manhoosbilli1/Iphone7-batteryless-MOD/qianli_reverse_engineering.kicad_sch

## KiCad design qianli_reverse_engineering.kicad_sch (2024-02-01)

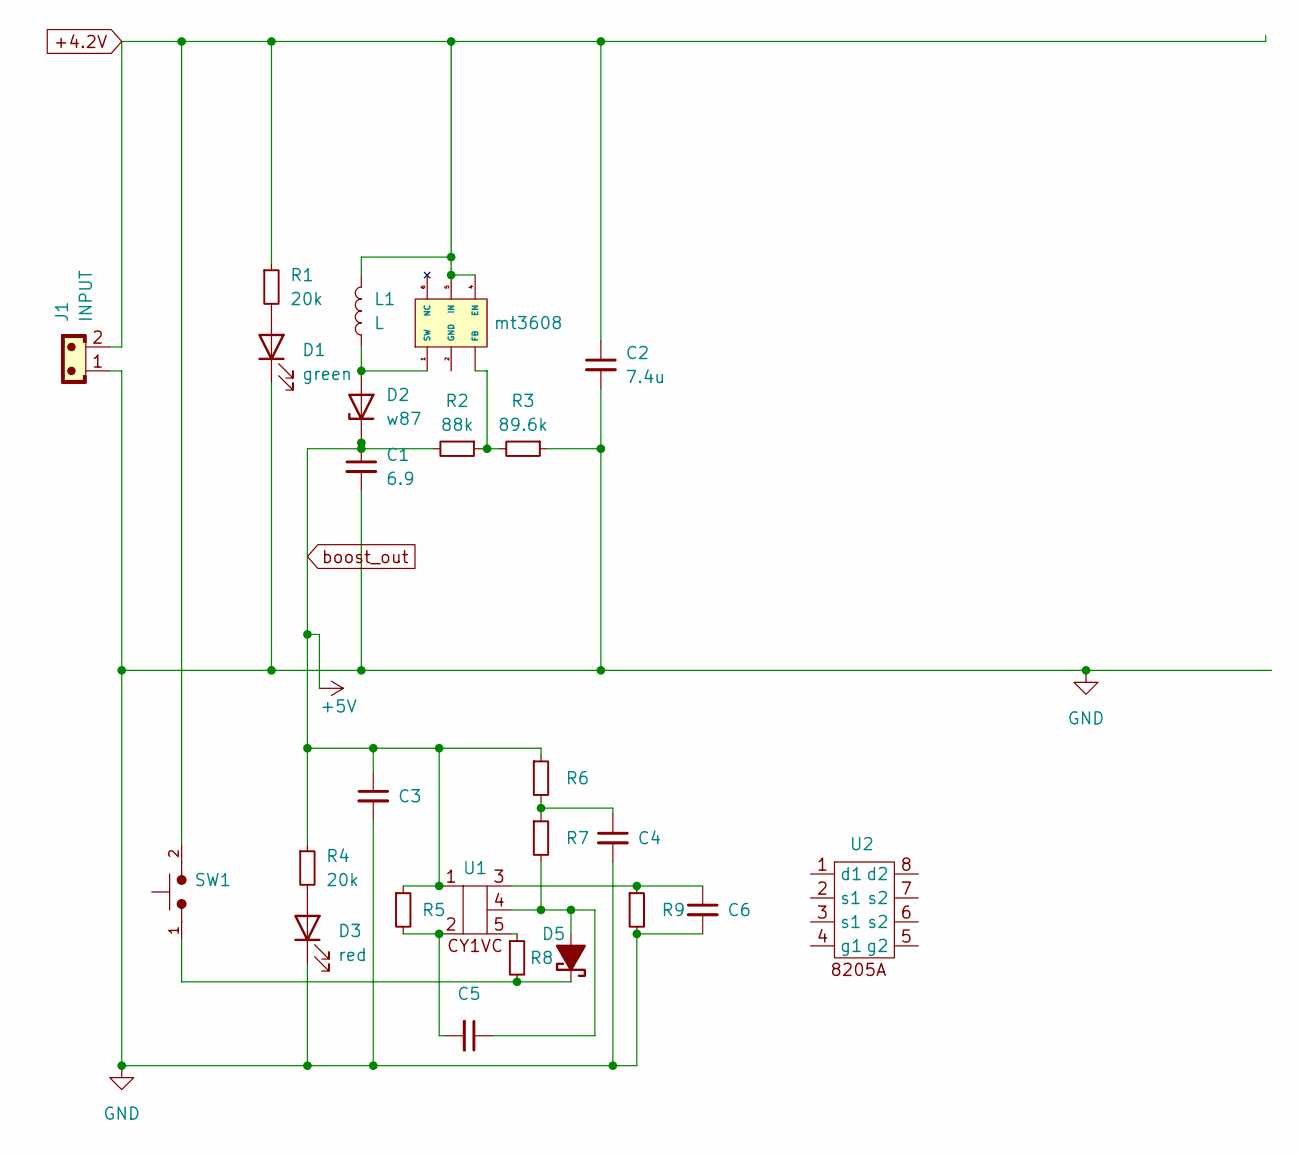
[picture p62: schematic qianli_reverse_engineering.kicad_sch]

Parts:
C1: 6.9
C2: 7.4u
C3, C4, C5, C6: (no value)
D1: green
D2: w87
D3: red
D5: D,Schottky,IEEE
J1: INPUT; JST_EH_B2B-EH-A_1x02_P2.50mm_Vertical
L1: L
R1, R4: 20k
R2: 88k
R3: 89.6k
R5, R6, R7, R8, R9: (no value)
SW1: Push_Button; SW_PUSH_6mm
U1, U2: (no value)
mt3608: (no value)

Connections:
+4.2V: C2.1, J1.2, L1.2, R1.1, SW1.2, mt3608.4 (EN), mt3608.5 (IN)
+5V: C1.1, C3.1, D2.1 (K), R2.2, R4.1, R5.1, R6.1, U1.1
GND: C1.2, C2.2, C3.2, C4.2, C6.2, D1.1 (K), D3.1 (K), J1.1, R3.1, R9.2
unnamed: C4.1, R6.2, R7.1
unnamed: C5.1, D5.2 (A+), R7.2, U1.4
unnamed: C5.2, R5.2, U1.2
unnamed: C6.1, R9.1, U1.3
unnamed: D1.2 (A), R1.2
unnamed: D2.2 (A), L1.1, mt3608.1 (SW)
unnamed: D3.2 (A), R4.2
unnamed: D5.1 (K-), R8.2, SW1.1
unnamed: R2.1, R3.2, mt3608. (FB)
unnamed: R8.1, U1.5
